Alexandru730/E-book-reader/Images/PCB.png

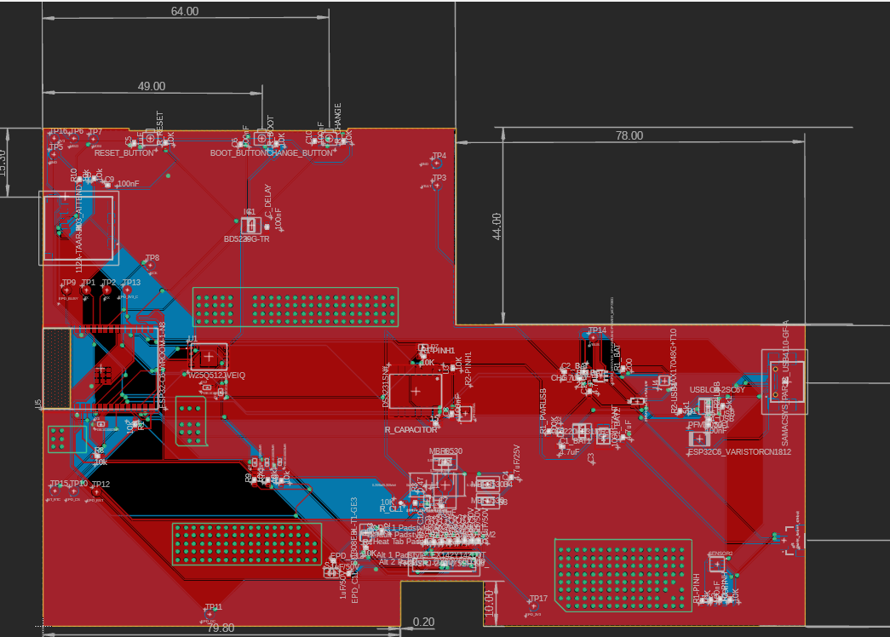
Images/PCB.png
