Alexandru730/E-book-reader/Images/produs3d_3.png

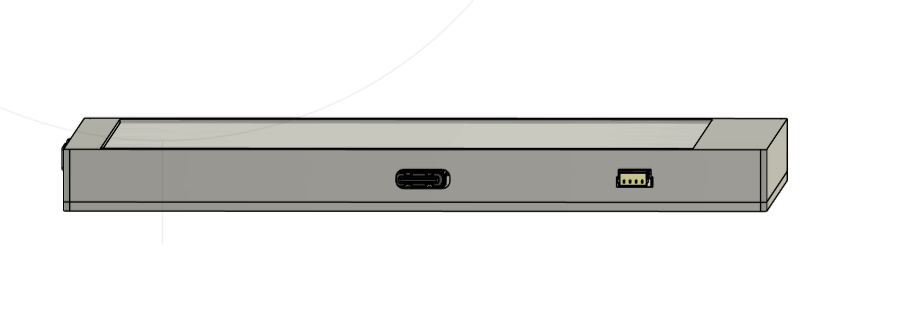
Images/produs3d_3.png
